haum/laumio/laumio/LaumioHttp.cpp

#include "LaumioHttp.h"

#include <ESP8266mDNS.h>

LaumioHttp::LaumioHttp(LaumioConfig &c, ESP8266WebServer &s)
    : server(s), config(c) {
	server.on("/", std::bind(&LaumioHttp::handleRoot, this));
	server.onNotFound(std::bind(&LaumioHttp::handleNotFound, this));
}

bool LaumioHttp::testCaptive(ESP8266WebServer &server) {
	String host = server.hostHeader();
	if (host != server.client().localIP().toString() &&
	    strcmp(".local", host.c_str() + host.length() - 6) &&
	    strcmp(".home", host.c_str() + host.length() - 5) &&
	    strcmp(".lan", host.c_str() + host.length() - 4)) {
		// The user is probably captured, redirect to my IP
		server.sendHeader("Cache-Control",
		                  "no-cache, no-store, must-revalidate");
		server.sendHeader("Pragma", "no-cache");
		server.sendHeader("Expires", "-1");
		server.sendHeader(
		    "Location", "http://" + server.client().localIP().toString() + "/",
		    true);
		server.send(302, "text/plain", "");
		return true;
	}
	return false;
}

void LaumioHttp::handleNotFound() {
	if (testCaptive(server))
		return;

	String message = "File Not Found\n\n";
	message += "URI: ";
	message += server.uri();
	message += "\nMethod: ";
	message += (server.method() == HTTP_GET) ? "GET" : "POST";
	message += "\nArguments: ";
	message += server.args();
	message += "\n";

	for (uint8_t i = 0; i < server.args(); i++) {
		message += " " + server.argName(i) + ": " + server.arg(i) + "\n";
	}

	server.send(404, "text/plain", message);
}

void LaumioHttp::handleRoot() {
	if (testCaptive(server))
		return;

	const auto html = R"(
<html>
	<head>
		<title>Laumio</title>
		<style>
			body { background: #eee; padding: 0; }
			section {
				margin: 0.1%;
				padding: 0.4%;
				float: left;
				width: 26%;
				height: 99%;
				background: #fff;
			}
			section.wide { width: 45%; }
			h1 { font-size: x-large; color: #CC8A4D; }
			h2 { font-size: large; color: #4D97CC; }
			a { color: #93859D; }
			form.form_sending input[type=submit] { color: #00aaaa; }
			form.form_failure input[type=submit] { color: #aa0000; }
			form.form_success input[type=submit] { color: #00aa00; }
			@media (max-width: 835px) {
				section, section.wide {
					float: none;
					width: 99%;
					height: auto;
				}
			}
		</style>
	</head>
	<body>
		<section>
			<h1>Laumio</h1>
			<h2>Hostname</h2>
			<input type="text" disabled="" value="^" />
			<h2>Uptime</h2>
			<input type="text" disabled="" value="^" />
			<h2>Links</h2>
			<p><a href="https://haum.org/pages/laumios.html">Project page</a></p>
			<p><a href="https://github.com/haum/laumio/">Source code</a></p>
			<p><a href="https://laumio.readthedocs.io/en/latest/">Documentation</a></p>
		</section>
		<section class="wide">
			<h1>Control</h1>
			<h2>Set pixel</h2>
			<form method="post" action="/api/">
				<input name="command" type="hidden" value="set_pixel" />
				<input name="led" type="number" min="0" max="13" placeholder="Led number" title="Led number" />
				<input name="rgb" type="color" title="Color" />
				<input type="submit" />
			</form>
			<h2>Set ring</h2>
			<form method="post" action="/api/">
				<input name="command" type="hidden" value="set_ring" />
				<input name="ring" type="number" min="0" max="2" placeholder="Ring number" title="Ring number" />
				<input name="rgb" type="color" title="Color" />
				<input type="submit" />
			</form>
			<h2>Set column</h2>
			<form method="post" action="/api/">
				<input name="command" type="hidden" value="set_column" />
				<input name="column" type="number" min="0" max="3" placeholder="Column number" title="Column number" />
				<input name="rgb" type="color" title="Color" />
				<input type="submit" />
			</form>
			<h2>Color wipe</h2>
			<form method="post" action="/api/">
				<input name="command" type="hidden" value="color_wipe" />
				<input name="duration" type="number" min="0" placeholder="Duration" title="Duration" />
				<input name="rgb" type="color" title="Color" />
				<input type="submit" />
			</form>
			<h2>Animate rainbow</h2>
			<form method="post" action="/api/">
				<input name="command" type="hidden" value="animate_rainbow" />
				<input type="submit" />
			</form>
			<h2>Fill</h2>
			<form method="post" action="/api/">
				<input name="command" type="hidden" value="fill" />
				<input name="rgb" type="color" title="Color" />
				<input type="submit" />
			</form>
		</section>
		<section>
			<h1>Config</h1>
			<form method="post" action="/config/">
				<h2>Connect <input name="enabled" type="checkbox" title="Enable" ^/></h2>
				<input name="command" type="hidden" value="config_connect" />
				<input name="essid" type="text" placeholder="Essid" title="Essid" value="^" /><br/>
				<input name="password" type="password" placeholder="Password" title="Password" value="^" /><br/>
				<input type="submit" />
			</form>
			<form method="post" action="/config/">
				<h2>Access point <input name="enabled" type="checkbox" title="Enable" ^/></h2>
				<input name="command" type="hidden" value="config_ap" />
				<input name="essid" type="text" placeholder="Essid" title="Essid" value="^" /><br/>
				<input name="password" type="password" placeholder="Password" title="Password" value="^" /><br/>
				<input type="submit" />
			</form>
			<form method="post" action="/config/">
				<h2>Fallback access point <input name="enabled" type="checkbox" title="Enable" ^/></h2>
				<input name="command" type="hidden" value="config_apfallback" />
				<input type="submit" />
			</form>
			<form method="post" action="/config/">
				<h2>MQTT <input name="enabled" type="checkbox" title="Enable" ^/></h2>
				<input name="command" type="hidden" value="config_mqtt" />
				<input name="host" type="text" placeholder="Brocker address" title="Brocker address" value="^" /><br/>
				<input name="user" type="text" placeholder="User" title="User" value="^" /><br/>
				<input name="password" type="password" placeholder="Password" title="Password" value="^" /><br/>
				<input type="submit" />
			</form>
			<form method="post" action="/config/">
				<h2>Reboot</h2>
				<input name="command" type="hidden" value="reboot" />
				<input type="submit" />
			</form>
		</section>
		<script>
			forms = document.body.getElementsByTagName('form');
			for (var i = 0; i < forms.length; i++) {
				forms[i].onsubmit = function(e) {
					e.preventDefault();
					this.classList.add("form_sending");
					this.classList.remove("form_success");
					this.classList.remove("form_failure");
					var formData = new FormData(this);
					var xmlhttp;
					if (window.XMLHttpRequest) xmlhttp = new XMLHttpRequest();
					else xmlhttp = new ActiveXObject("Microsoft.XMLHTTP");
					xmlhttp.open("POST", this.action);
					xmlhttp.overrideMimeType('application/json');
					var form = this;
					xmlhttp.onreadystatechange = function () {
						if (xmlhttp.readyState == 4) {
							if(xmlhttp.status == 200) {
								json = JSON.parse(xmlhttp.responseText);
								if (json["status"] == "Success")
									form.classList.add("form_success");
								else
									form.classList.add("form_failure");
								form.classList.remove("form_sending");
							}
						}
					};
					xmlhttp.onerror = function () {
						form.classList.add("form_failure");
						form.classList.remove("form_sending");
					};
					xmlhttp.onabort = function () {
						form.classList.add("form_failure");
						form.classList.remove("form_sending");
					};
					xmlhttp.send(formData);
				};
			}
		</script>
	</body>
</html>)";

	auto dynData = [&](char *buffer, int buffersz, int nb) {
		switch (nb) {
		case 0:
			WiFi.hostname().toCharArray(buffer, buffersz);
			break;

		case 1: {
			int sec = millis() / 1000;
			int min = sec / 60;
			int hr = min / 60;
			sprintf(buffer, "%02d:%02d:%02d", hr, min % 60, sec % 60);
		} break;

		case 2:
			if (config.connect_enabled)
				strcpy(buffer, R"(checked="checked" )");
			break;

		case 3:
			strcpy(buffer, config.connect_essid.value());
			break;

		case 4:
			strcpy(buffer, config.connect_password.value());
			break;

		case 5:
			if (config.ap_enabled)
				strcpy(buffer, R"(checked="checked" )");
			break;

		case 6:
			strcpy(buffer, config.ap_essid.value());
			break;

		case 7:
			strcpy(buffer, config.ap_password.value());
			break;

		case 8:
			if (config.apfallback_enabled)
				strcpy(buffer, R"(checked="checked" )");
			break;

		case 9:
			if (config.mqtt_enabled)
				strcpy(buffer, R"(checked="checked" )");
			break;

		case 10:
			strcpy(buffer, config.mqtt_host.value());
			break;

		case 11:
			strcpy(buffer, config.mqtt_user.value());
			break;

		case 12:
			strcpy(buffer, config.mqtt_password.value());
			break;
		}
	};

	// Send html string, and call dynData(...) to replace each '^'.
	char buffer[512];
	server.setContentLength(CONTENT_LENGTH_UNKNOWN);
	server.send(200, "text/html", ""); // Send headers
	int dynDataNb = 0;
	const char *const htmlend = html + strlen(html);
	const char *htmlsend = html;
	const char *it = htmlsend - 1;
	while (htmlsend < htmlend - 1) {
		if (it <= htmlsend + 1) {
			it = std::find(it + 1, htmlend, '^');
		}
		int vol = it - htmlsend - 1;
		vol = std::min(vol, int(sizeof(buffer) - 1));
		memcpy(buffer, htmlsend + 1, vol);
		buffer[vol] = 0;
		htmlsend += vol;
		server.sendContent(buffer);
		if (it <= htmlsend + 1 && it != htmlend) {
			buffer[0] = 0;
			dynData(buffer, sizeof(buffer), dynDataNb);
			dynDataNb++;
			if (buffer[0])
				server.sendContent(buffer);
			htmlsend += 1;
		}
	}
}
