haum/laumio/laumio/LaumioLeds.cpp

#include "LaumioLeds.h"

const LaumioLeds::Led LaumioLeds::LowerRing[4] = {A_Bottom, B_Bottom, C_Bottom,
                                                  D_Bottom};

const LaumioLeds::Led LaumioLeds::MiddleRing[4] = {A_Middle, B_Middle, C_Middle,
                                                   D_Middle};

const LaumioLeds::Led LaumioLeds::UpperRing[4] = {A_Top, B_Top, C_Top, D_Top};

const LaumioLeds::Led LaumioLeds::AColumn[3] = {A_Bottom, A_Middle, A_Top};

const LaumioLeds::Led LaumioLeds::BColumn[3] = {B_Bottom, B_Middle, B_Top};

const LaumioLeds::Led LaumioLeds::CColumn[3] = {C_Bottom, C_Middle, C_Top};

const LaumioLeds::Led LaumioLeds::DColumn[3] = {D_Bottom, D_Middle, D_Top};

LaumioLeds::LaumioLeds(uint16_t n, uint8_t p) : strip(n, p) {}

void LaumioLeds::begin() {
	strip.begin();
	strip.show();
}

int LaumioLeds::count() { return strip.numPixels(); }

void LaumioLeds::setPixelColor(const int led, const uint8_t &r,
                               const uint8_t &g, const uint8_t &b) {
	if (led < strip.numPixels()) {
		strip.setPixelColor(led, r, g, b);
	}
}

void LaumioLeds::setRingColor(int ring, uint8_t r, uint8_t g, uint8_t b) {
	LaumioLeds::Led *pring = nullptr;
	switch (ring) {
	case 0:
		pring = (LaumioLeds::Led *)&LaumioLeds::LowerRing;
		break;
	case 1:
		pring = (LaumioLeds::Led *)&LaumioLeds::MiddleRing;
		break;
	case 2:
		pring = (LaumioLeds::Led *)&LaumioLeds::UpperRing;
		break;
	}

	if (pring) {
		for (int i = 0; i < 4; i++) {
			strip.setPixelColor(pring[i], r, g, b);
		}
	}
}

void LaumioLeds::setColumnColor(int column, uint8_t r, uint8_t g, uint8_t b) {
	LaumioLeds::Led *pcolumn = nullptr;
	switch (column) {
	case 0:
		pcolumn = (LaumioLeds::Led *)&LaumioLeds::AColumn;
		break;
	case 1:
		pcolumn = (LaumioLeds::Led *)&LaumioLeds::BColumn;
		break;
	case 2:
		pcolumn = (LaumioLeds::Led *)&LaumioLeds::CColumn;
		break;
	case 3:
		pcolumn = (LaumioLeds::Led *)&LaumioLeds::DColumn;
		break;
	}

	if (pcolumn) {
		for (int i = 0; i < 3; i++) {
			strip.setPixelColor(pcolumn[i], r, g, b);
		}
	}
}

void LaumioLeds::fillColor(const uint8_t &r, const uint8_t &g,
                           const uint8_t &b) {
	for (uint16_t i = 0; i < strip.numPixels(); i++) {
		strip.setPixelColor(i, r, g, b);
	}
}

void LaumioLeds::show() { strip.show(); }

void LaumioLeds::animate(Animation a) {
	switch (a) {
	case Animation::Clear:
		colorWipe(strip.Color(0, 0, 0), 50);
		break;
	case Animation::Hello:
		colorWipe(strip.Color(255, 0, 255), 50);
		colorWipe(strip.Color(0, 0, 0), 50);
		break;
	case Animation::Loading:
		colorWipe(strip.Color(255, 0, 0), 50);
		colorWipe(strip.Color(0, 0, 0), 50);
		break;
	case Animation::Happy:
		rainbowCycle(1);
		break;
	}
}

// Fill the dots one after the other with a color
void LaumioLeds::colorWipe(uint32_t c, uint8_t wait) {
	uint16_t i;
	for (i = 0; i < strip.numPixels(); i++) {
		strip.setPixelColor(i, c);
		strip.show();
		delay(wait);
	}
}

// Slightly different, this makes the rainbow equally distributed throughout
void LaumioLeds::rainbowCycle(uint8_t wait) {
	uint16_t i, j;
	for (j = 0; j < 256 * 5; j++) { // 5 cycles of all colors on wheel
		for (i = 0; i < strip.numPixels(); i++) {
			strip.setPixelColor(
			    i, wheel(((i * 256 / strip.numPixels()) + j) & 255));
		}
		strip.show();
		delay(wait);
	}
}

// Input a value 0 to 255 to get a color value.
// The colours are a transition r - g - b - back to r.
uint32_t LaumioLeds::wheel(byte wheelPos) {
	wheelPos = 255 - wheelPos;
	if (wheelPos < 85) {
		return strip.Color(255 - wheelPos * 3, 0, wheelPos * 3);
	}
	if (wheelPos < 170) {
		wheelPos -= 85;
		return strip.Color(0, wheelPos * 3, 255 - wheelPos * 3);
	}
	wheelPos -= 170;
	return strip.Color(wheelPos * 3, 255 - wheelPos * 3, 0);
}

bool LaumioLeds::jsonCommands(const char *str) {
	StaticJsonDocument<800> jsonBuffer;
	auto deserializeStatus = deserializeJson(jsonBuffer, str);
	return (deserializeStatus == DeserializationError::Ok) && jsonCommands(jsonBuffer.as<JsonObject>());
}

bool LaumioLeds::jsonCommands(JsonObject jo) {
	if (jo.containsKey("commands")) {
		if (!jo["commands"].is<JsonArray>())
			return false;
		bool ok = true;
		for (auto var : jo["commands"].as<JsonArray>())
			ok &= jsonCommands(var.as<JsonObject>());
		return ok;

	} else if (jo.containsKey("command")) {
		const auto &cmd = jo["command"];

		int r = jo["rgb"][0];
		int g = jo["rgb"][1];
		int b = jo["rgb"][2];
		if (jo["rgb"].is<const char *>()) {
			const char * colorstr = jo["rgb"];
			if (colorstr[0] == '#' && strlen(colorstr) == 7) {
				int color = strtol(colorstr + 1, nullptr, 16);
				r = (color >> 16) & 0xff;
				g = (color >> 8) & 0xff;
				b = color & 0xff;
			}
		}

		if (cmd == "set_pixel") {
			setPixelColor(jo["led"], r, g, b);
			show();
			return true;
		} else if (cmd == "set_ring") {
			setRingColor(jo["ring"], r, g, b);
			show();
			return true;
		} else if (cmd == "set_column") {
			setColumnColor(jo["column"], r, g, b);
			show();
			return true;
		} else if (cmd == "color_wipe") {
			colorWipe(strip.Color(r, g, b), jo["duration"]);
			return true;
		} else if (cmd == "animate_rainbow") {
			rainbowCycle(1);
			return true;
		} else if (cmd == "fill") {
			fillColor(r, g, b);
			show();
			return true;
		}

	} else if (jo.containsKey("rgb")) { // Legacy api
		const int led = jo["led"];
		const int r = jo["rgb"][0];
		const int g = jo["rgb"][1];
		const int b = jo["rgb"][2];

		// if led = 255 set all LEDs to rgb value
		if (led == 255) {
			fillColor(r, g, b);
		} else {
			setPixelColor(led, r, g, b);
		}
		show();
		return true;
	}
	return false;
}
